ttqq2330arch/-Desktop-Monitoring-Status-Clock/esp32/src/clock_fonts.h

// 自动生成：翻页时钟数字掩码（多字体 · 4-bit alpha 抗锯齿）。
// 由 tools/gen_clock_font.py 生成，请勿手改。
// 值域 0..15：0=纯背景，15=纯墨迹，中间为边缘覆盖度。
// 固件：短按按键切页，长按按键循环切换字体（CLOCK_FONT_COUNT 套）。
// 每套字体的 (size, BOLD_R) 经实测定标流程确定：
//   约束 = 墨迹高度≈23~24px 且所有数字左右各留 >=1px（20px 数列内不裁边）。
#pragma once
#include <stdint.h>

#define CLOCK_FONT_W 18
#define CLOCK_FONT_H 58
#define CLOCK_FONT_A_MAX 15
#define CLOCK_FONT_COUNT 4

// 字体名（切换时显示在屏幕上，便于辨认当前用的是哪一套）
static const char* const CLOCK_FONT_NAME[CLOCK_FONT_COUNT] = {
  "Fredoka", "Nunito", "Poppins", "Trebuchet"
};

// [字体][数字][行][列]，行优先。
static const uint8_t CLOCK_FONTS[CLOCK_FONT_COUNT][10][58][18] PROGMEM = {
  {  // [0] Fredoka  size=41 BOLD_R=2 inkH=48 ink=55.2%
    {  // digit 0
      {0, 0, 0, 0, 0, 0, 0, 0, 0, 0, 0, 0, 0, 0, 0, 0, 0, 0},
      {0, 0, 0, 0, 0, 0, 0, 0, 0, 0, 0, 0, 0, 0, 0, 0, 0, 0},
      {0, 0, 0, 0, 0, 0, 0, 0, 0, 0, 0, 0, 0, 0, 0, 0, 0, 0},
      {0, 0, 0, 0, 0, 0, 0, 0, 0, 0, 0, 0, 0, 0, 0, 0, 0, 0},
      {0, 0, 0, 0, 0, 0, 0, 0, 0, 0, 0, 0, 0, 0, 0, 0, 0, 0},
      {0, 0, 0, 0, 0, 0, 0, 0, 0, 0, 0, 0, 0, 0, 0, 0, 0, 0},
      {0, 0, 0, 0, 0, 0, 0, 0, 0, 0, 0, 0, 0, 0, 0, 0, 0, 0},
      {0, 0, 0, 0, 0, 0, 0, 0, 2, 2, 0, 0, 0, 0, 0, 0, 0, 0},
      {0, 0, 0, 0, 0, 0, 8, 13, 14, 14, 13, 8, 0, 0, 0, 0, 0, 0},
      {0, 0, 0, 0, 0, 11, 15, 15, 15, 15, 15, 15, 11, 0, 0, 0, 0, 0},
      {0, 0, 0, 0, 9, 15, 15, 15, 15, 15, 15, 15, 15, 9, 0, 0, 0, 0},
      {0, 0, 0, 3, 15, 15, 15, 15, 15, 15, 15, 15, 15, 15, 4, 0, 0, 0},
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
      {0, 4, 15, 15, 15, 15, 10, 0, 0, 0, 0, 10, 15, 15, 15, 15, 4, 0},
      {0, 4, 15, 15, 15, 15, 13, 0, 0, 0, 0, 13, 15, 15, 15, 15, 4, 0},
      {0, 4, 15, 15, 15, 15, 15, 4, 0, 0, 4, 15, 15, 15, 15, 15, 4, 0},
      {0, 4, 15, 15, 15, 15, 15, 12, 0, 0, 12, 15, 15, 15, 15, 15, 4, 0},
      {0, 3, 15, 15, 15, 15, 15, 15, 11, 12, 15, 15, 15, 15, 15, 15, 4, 0},
      {0, 1, 14, 15, 15, 15, 15, 15, 15, 15, 15, 15, 15, 15, 15, 15, 4, 0},
      {0, 0, 12, 15, 15, 15, 15, 15, 15, 15, 15, 15, 15, 15, 15, 15, 4, 0},
      {0, 0, 8, 15, 15, 15, 15, 15, 15, 15, 15, 15, 15, 15, 15, 15, 4, 0},
      {0, 0, 3, 15, 15, 15, 15, 15, 15, 15, 15, 15, 15, 15, 15, 15, 4, 0},
      {0, 0, 0, 11, 15, 15, 15, 15, 15, 15, 15, 15, 15, 15, 15, 15, 3, 0},
      {0, 0, 0, 4, 15, 15, 15, 15, 15, 15, 15, 15, 15, 15, 15, 14, 1, 0},
      {0, 0, 0, 0, 8, 15, 15, 15, 15, 15, 15, 15, 15, 15, 15, 13, 0, 0},
      {0, 0, 0, 0, 0, 8, 14, 15, 15, 15, 15, 15, 15, 15, 15, 10, 0, 0},
      {0, 0, 0, 0, 0, 0, 2, 6, 6, 9, 15, 15, 15, 15, 15, 8, 0, 0},
      {0, 0, 0, 0, 0, 0, 0, 0, 0, 9, 15, 15, 15, 15, 15, 4, 0, 0},
      {0, 0, 0, 0, 0, 0, 0, 0, 1, 14, 15, 15, 15, 15, 14, 1, 0, 0},
      {0, 0, 0, 0, 0, 0, 0, 0, 6, 15, 15, 15, 15, 15, 11, 0, 0, 0},
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
    }
  }
};
